leonardoward/Atlas-Sumo-Robot/3D_Models/Sumo Modelo 1.jpg

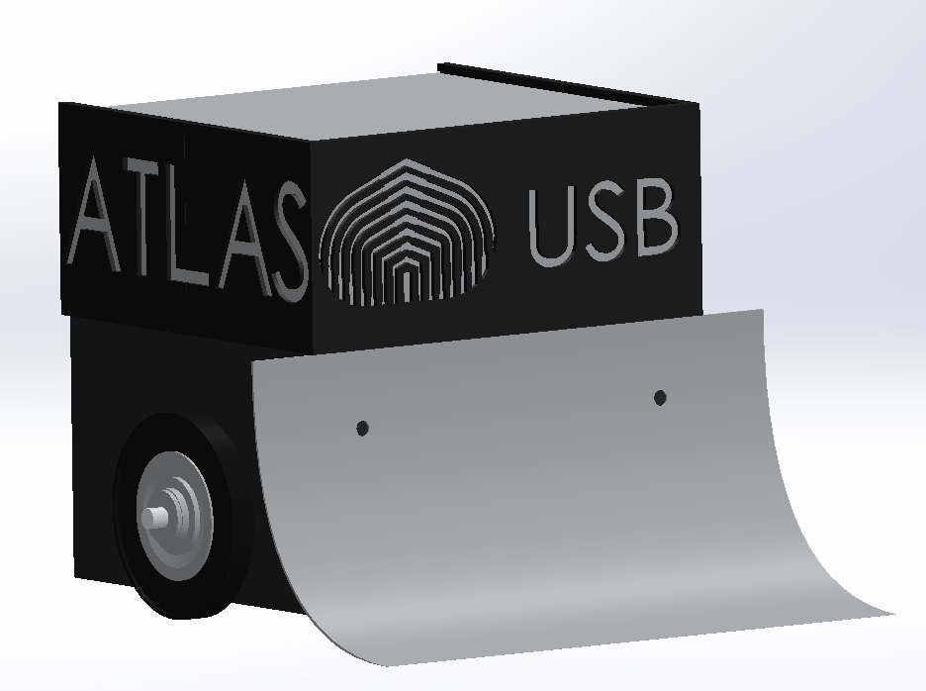
3D_Models/Sumo Modelo 1.jpg
