leonardoward/Atlas-Sumo-Robot/3D_Models/Sumo Modelo 2.jpg

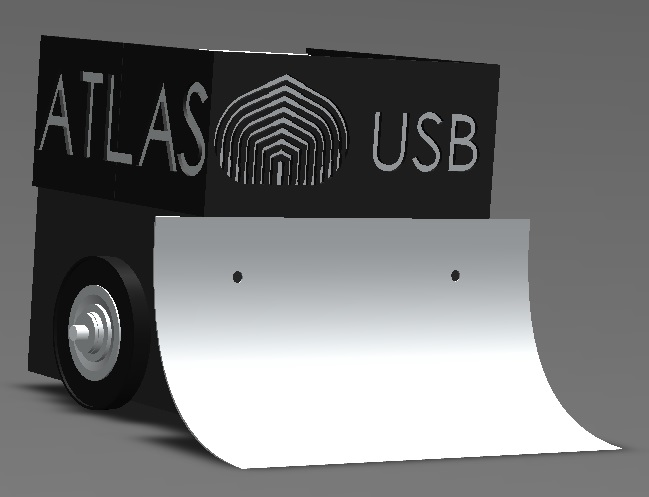
3D_Models/Sumo Modelo 2.jpg
