leonardoward/Atlas-Sumo-Robot/3D_Models/Sumo Modelo 3.jpg

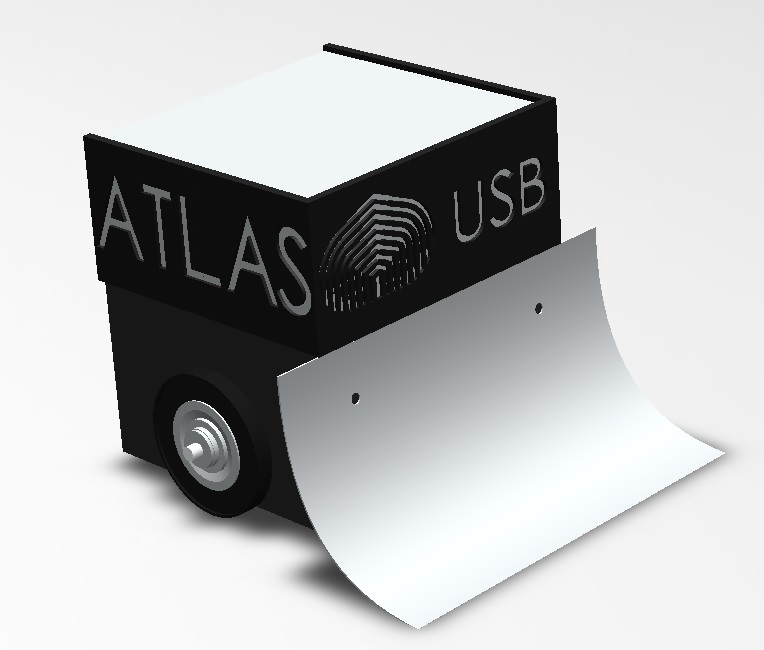
3D_Models/Sumo Modelo 3.jpg
