leonardoward/Atlas-Sumo-Robot/3D_Models/Sumo Modelo 4.jpg

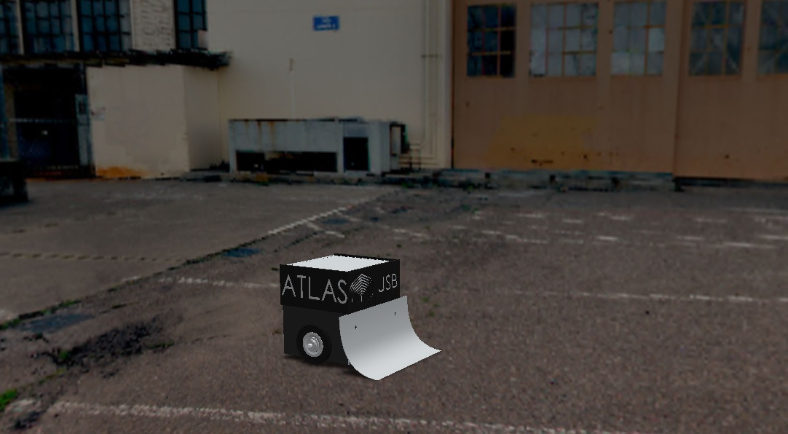
3D_Models/Sumo Modelo 4.jpg
