leonardoward/Atlas-Sumo-Robot/3D_Models/Sumo Modelo 5.jpg

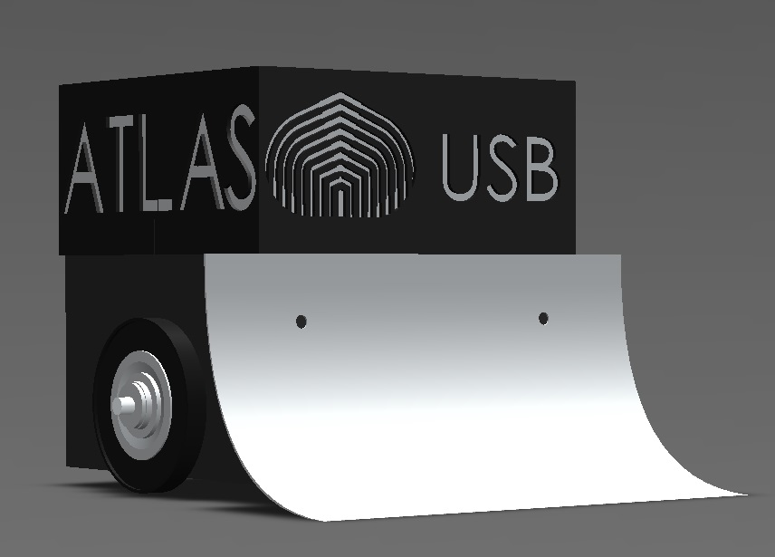
3D_Models/Sumo Modelo 5.jpg
