leonardoward/Atlas-Sumo-Robot/3D_Models/Sumo Modelo 6.jpg

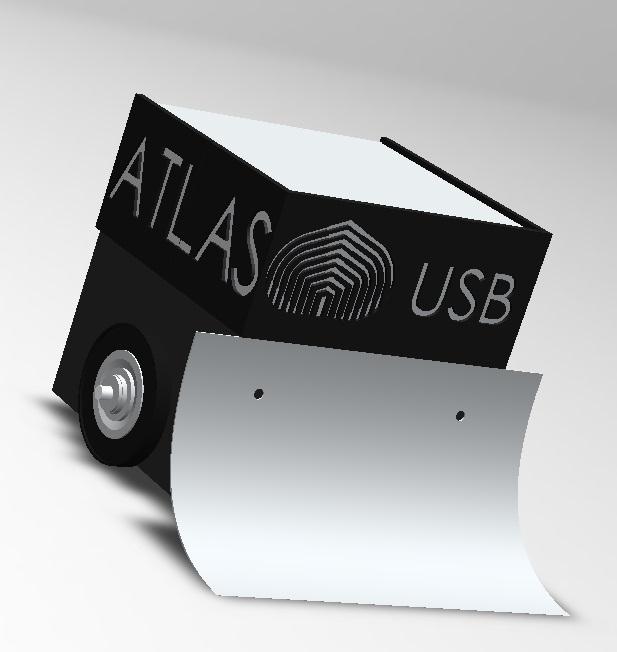
3D_Models/Sumo Modelo 6.jpg
