leonardoward/Atlas-Sumo-Robot/Pista Sumo.png

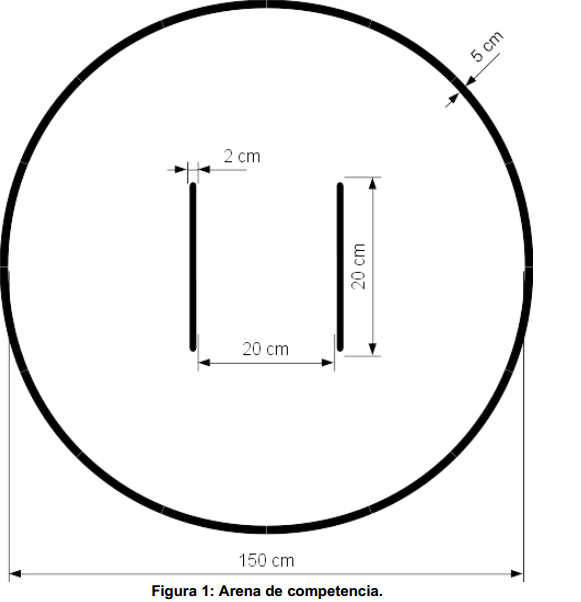
Pista Sumo.png
