leonardoward/Atlas-Sumo-Robot/3D_Models/Caja y rueda/Pieza N°3.SLDPRT

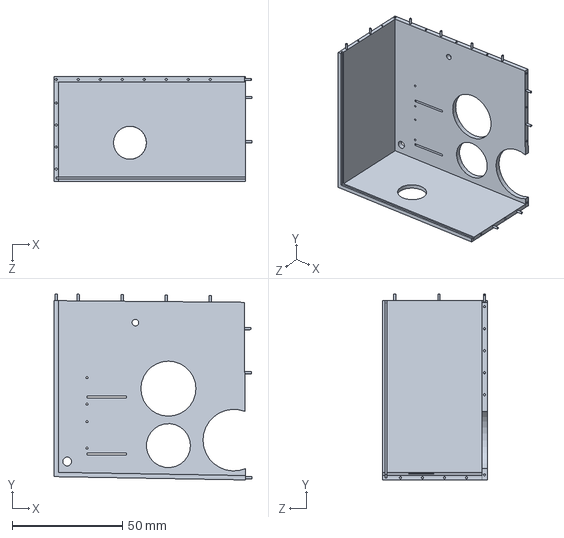
[picture p33: CAD file, 2019-05-23]
3D_Models/Caja y rueda/Pieza N°3.SLDPRT
90.0 x 84.5 x 47.5 mm
