leonardoward/Atlas-Sumo-Robot/3D_Models/Electronica/3xNanoV3.0ATmega328.SLDPRT

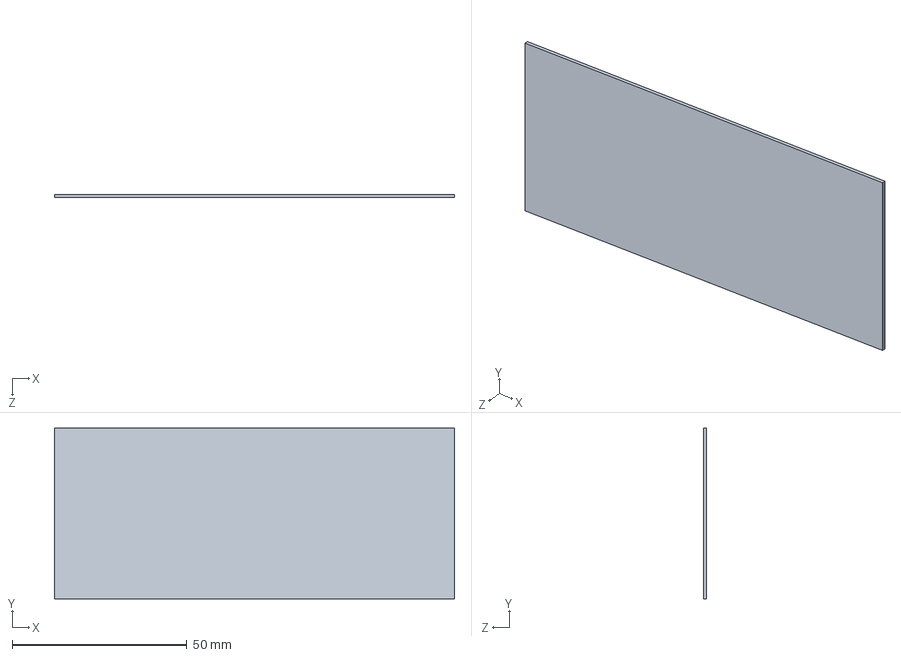
[picture p34: CAD file, 2019-05-23]
3D_Models/Electronica/3xNanoV3.0ATmega328.SLDPRT
114.3 x 48.8 x 1.00 mm
