leonardoward/Atlas-Sumo-Robot/3D_Models/Rampa Alternativa/Tubo.SLDPRT

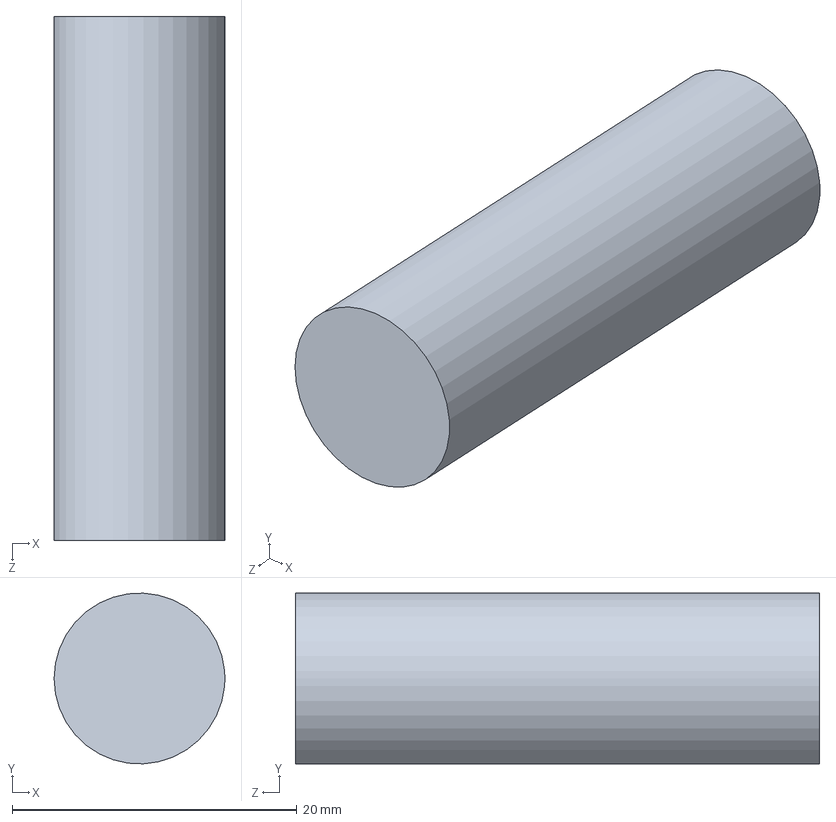
[picture p35: CAD file, 2019-05-23]
3D_Models/Rampa Alternativa/Tubo.SLDPRT
12.0 x 12.0 x 36.8 mm
