leonardoward/Atlas-Sumo-Robot/3D_Models/Version 3/EngranajeNegroCentralModificado.SLDPRT

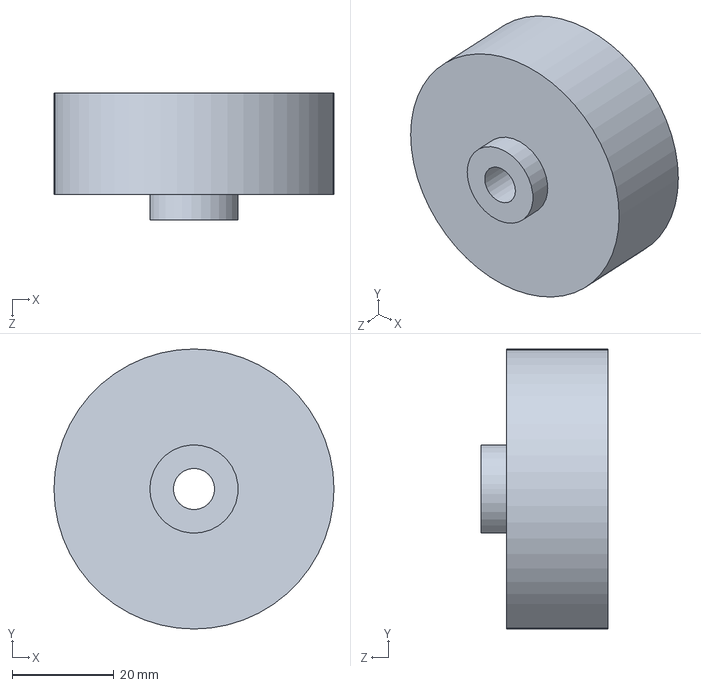
[picture p36: CAD file, 2019-05-23]
3D_Models/Version 3/EngranajeNegroCentralModificado.SLDPRT
55.0 x 55.0 x 25.0 mm
