leonardoward/Atlas-Sumo-Robot/3D_Models/Caja y rueda/Pieza N°4.SLDPRT

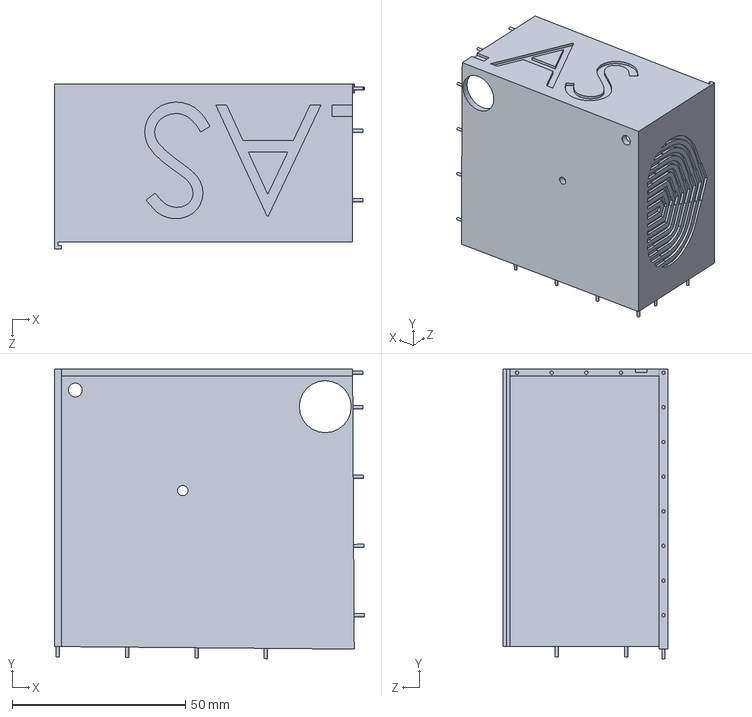
[picture p37: CAD file, 2019-05-23]
3D_Models/Caja y rueda/Pieza N°4.SLDPRT
89.4 x 83.5 x 47.5 mm
