leonardoward/Atlas-Sumo-Robot/3D_Models/Electronica/RollerBallTransfer(rueda loca).SLDPRT

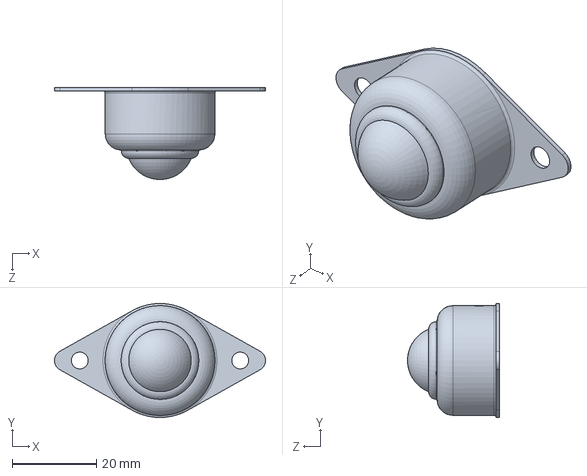
[picture p38: CAD file, 2019-05-23]
3D_Models/Electronica/RollerBallTransfer(rueda loca).SLDPRT
50.0 x 27.0 x 21.8 mm
