leonardoward/Atlas-Sumo-Robot/3D_Models/Version 3/BaseMotorDeSumo.SLDPRT

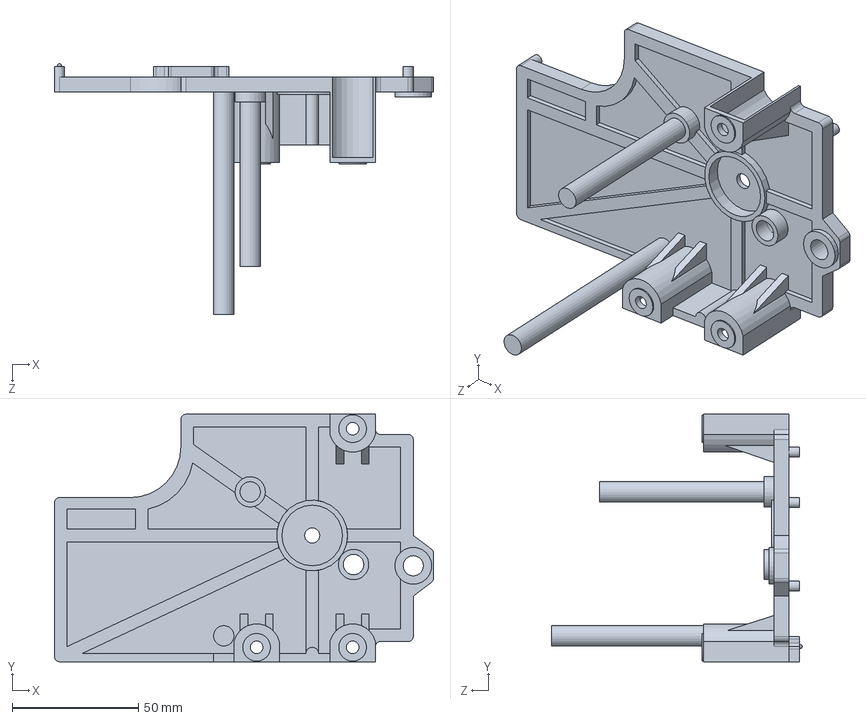
[picture p39: CAD file, 2019-05-23]
3D_Models/Version 3/BaseMotorDeSumo.SLDPRT
150.0 x 98.0 x 99.2 mm
