leonardoward/Atlas-Sumo-Robot/3D_Models/Electronica/LogicLevelShifter,4-Channel,Bidirectional.SLDPRT

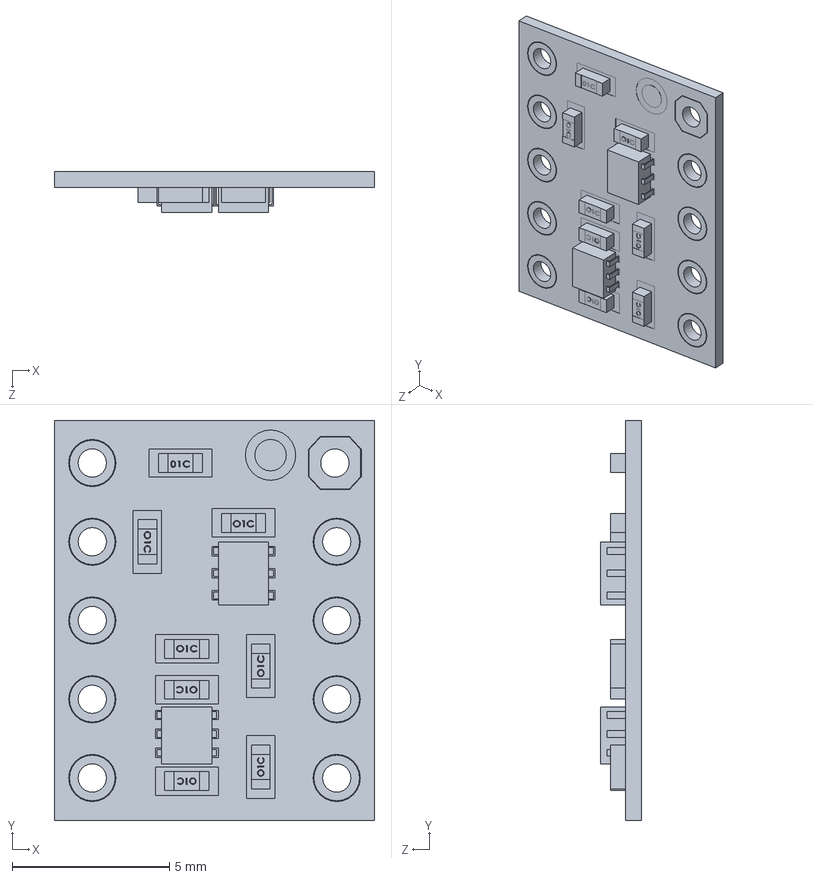
[picture p40: CAD file, 2019-05-23]
3D_Models/Electronica/LogicLevelShifter,4-Channel,Bidirectional.SLDPRT
10.2 x 12.7 x 1.30 mm
