leonardoward/Atlas-Sumo-Robot/3D_Models/Version 3/Viga.SLDPRT

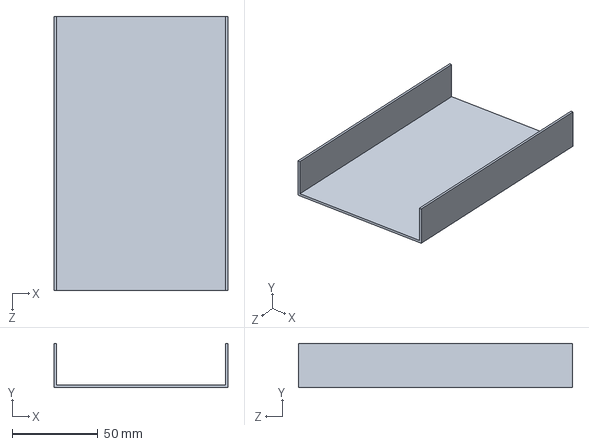
[picture p41: CAD file, 2019-05-23]
3D_Models/Version 3/Viga.SLDPRT
101.5 x 25.7 x 160.0 mm
