leonardoward/Atlas-Sumo-Robot/3D_Models/Electronica/Pololu5V,2.5AStep-DownVoltageRegulatorD24V22F5.SLDPRT

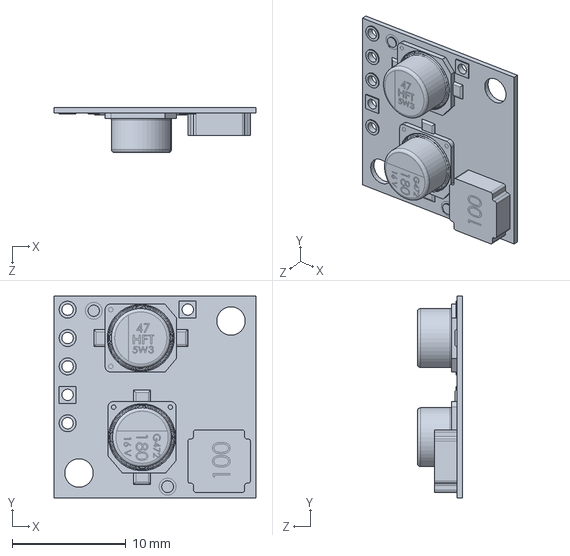
[picture p42: CAD file, 2019-05-23]
3D_Models/Electronica/Pololu5V,2.5AStep-DownVoltageRegulatorD24V22F5.SLDPRT
17.8 x 17.8 x 4.00 mm
