leonardoward/Atlas-Sumo-Robot/3D_Models/Version 3/MotorDeSumo.SLDPRT

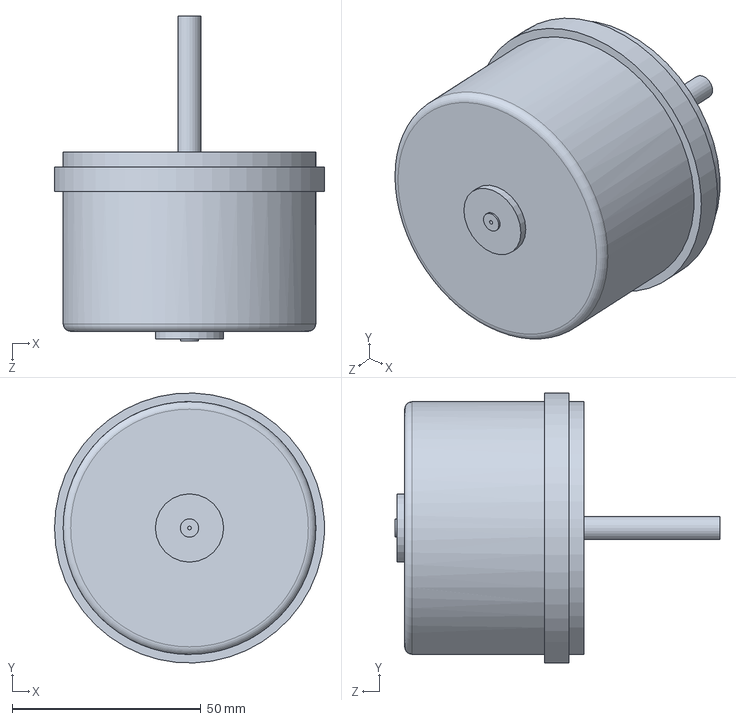
[picture p43: CAD file, 2019-05-23]
3D_Models/Version 3/MotorDeSumo.SLDPRT
71.5 x 71.5 x 86.0 mm
