leonardoward/Atlas-Sumo-Robot/3D_Models/Electronica/QTR-1AReflectanceSensor.SLDPRT

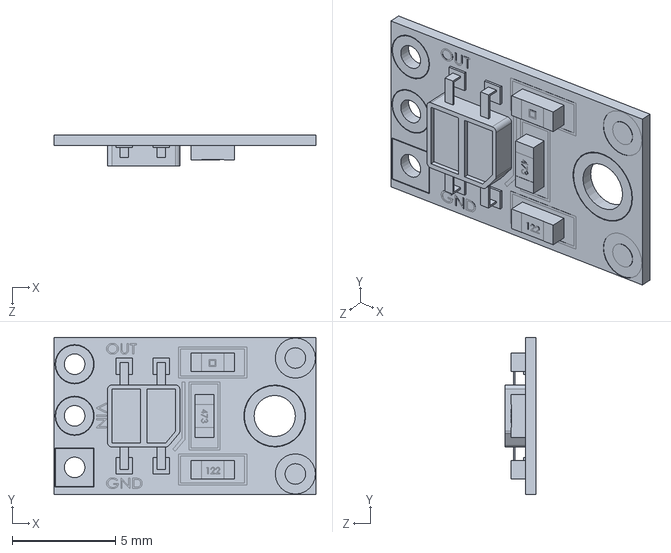
[picture p44: CAD file, 2019-05-23]
3D_Models/Electronica/QTR-1AReflectanceSensor.SLDPRT
12.7 x 7.62 x 1.50 mm
