leonardoward/Atlas-Sumo-Robot/3D_Models/Version 3/RuedaNueva.SLDPRT

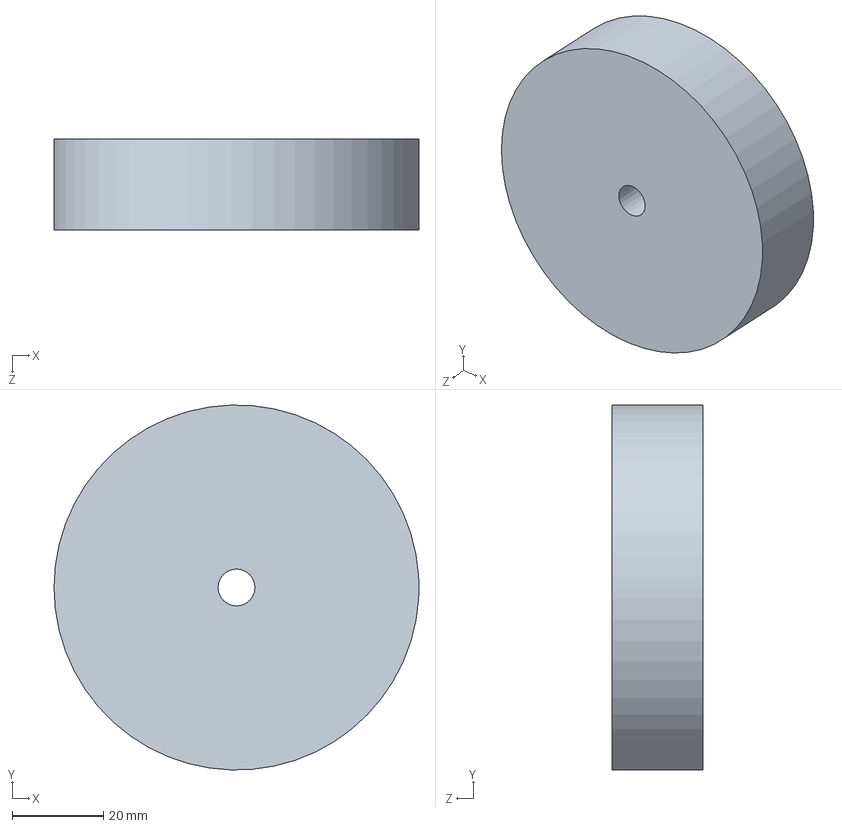
[picture p45: CAD file, 2019-05-23]
3D_Models/Version 3/RuedaNueva.SLDPRT
80.0 x 80.0 x 20.0 mm
