leonardoward/Atlas-Sumo-Robot/3D_Models/Electronica/PololuAdjustable9-30VStep-UpVoltageRegulatorU3V50AHV.SLDPRT

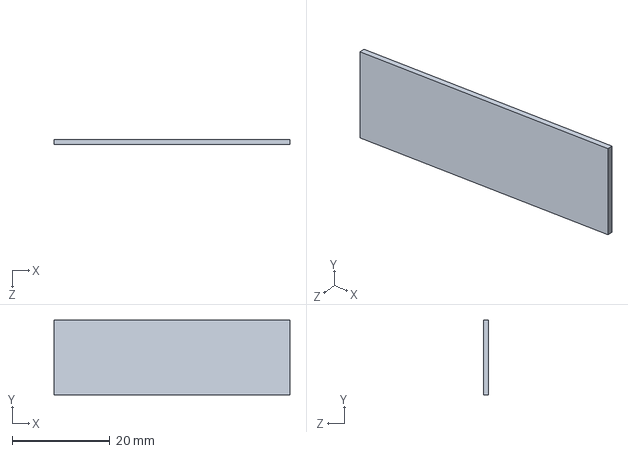
[picture p46: CAD file, 2019-05-23]
3D_Models/Electronica/PololuAdjustable9-30VStep-UpVoltageRegulatorU3V50AHV.SLDPRT
48.3 x 15.2 x 1.00 mm
