leonardoward/Atlas-Sumo-Robot/3D_Models/Electronica/LiPoBattery.SLDPRT

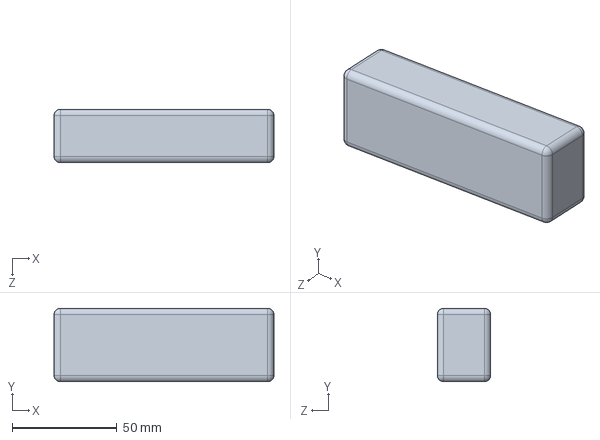
[picture p47: CAD file, 2019-05-23]
3D_Models/Electronica/LiPoBattery.SLDPRT
104.8 x 34.9 x 25.4 mm
