leonardoward/Atlas-Sumo-Robot/Electronics_Design/Electronica/Pololu step-up voltage regulator U3V50x, bottom view with dimensions.jpg

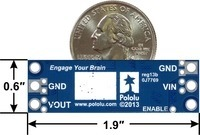
Electronics_Design/Electronica/Pololu step-up voltage regulator U3V50x, bottom view with dimensions.jpg
