leonardoward/Atlas-Sumo-Robot/3D_Models/Version 3/PDF/2.Chasis2.PDF

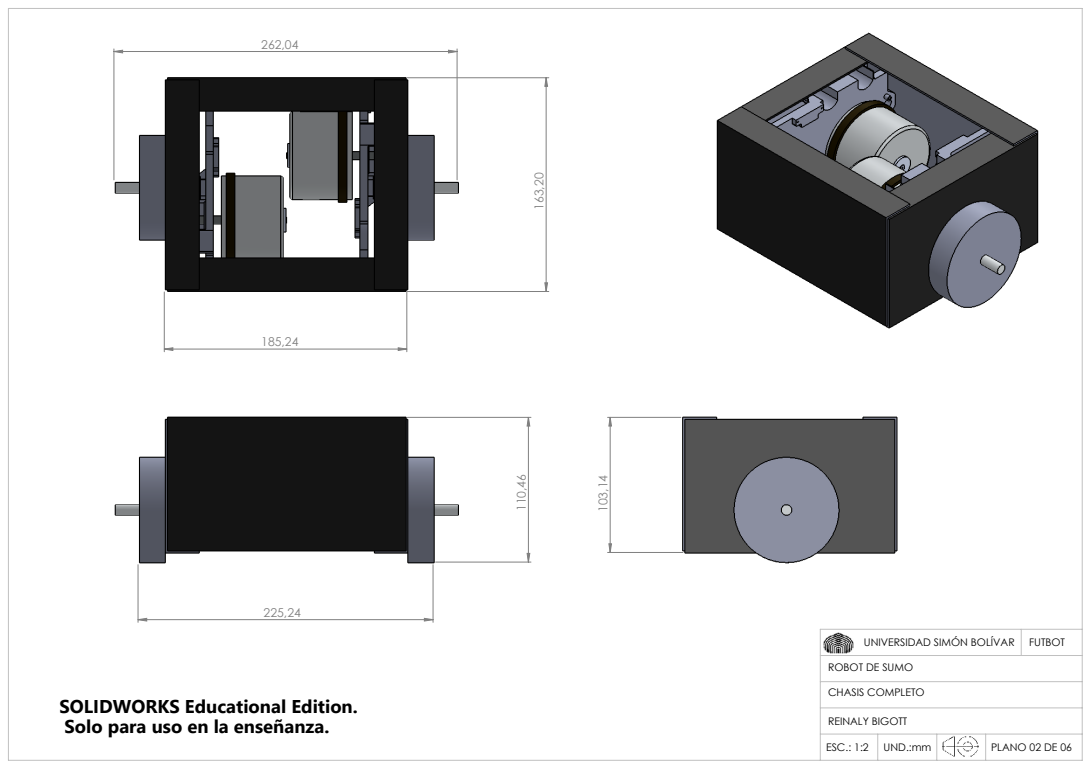
[picture p62: page 1]
UNIVERSIDAD SIMÓN BOLÍVAR; FUTBOT; REINALY BIGOTT; ESC.: 1:2; UND.:mm; PLANO 02 DE 06

ROBOT DE SUMO
CHASIS COMPLETO

SOLIDWORKS Educational Edition.
Solo para uso en la enseñanza.
