leonardoward/Atlas-Sumo-Robot/3D_Models/Version 3/PDF/3.Chasis3.PDF

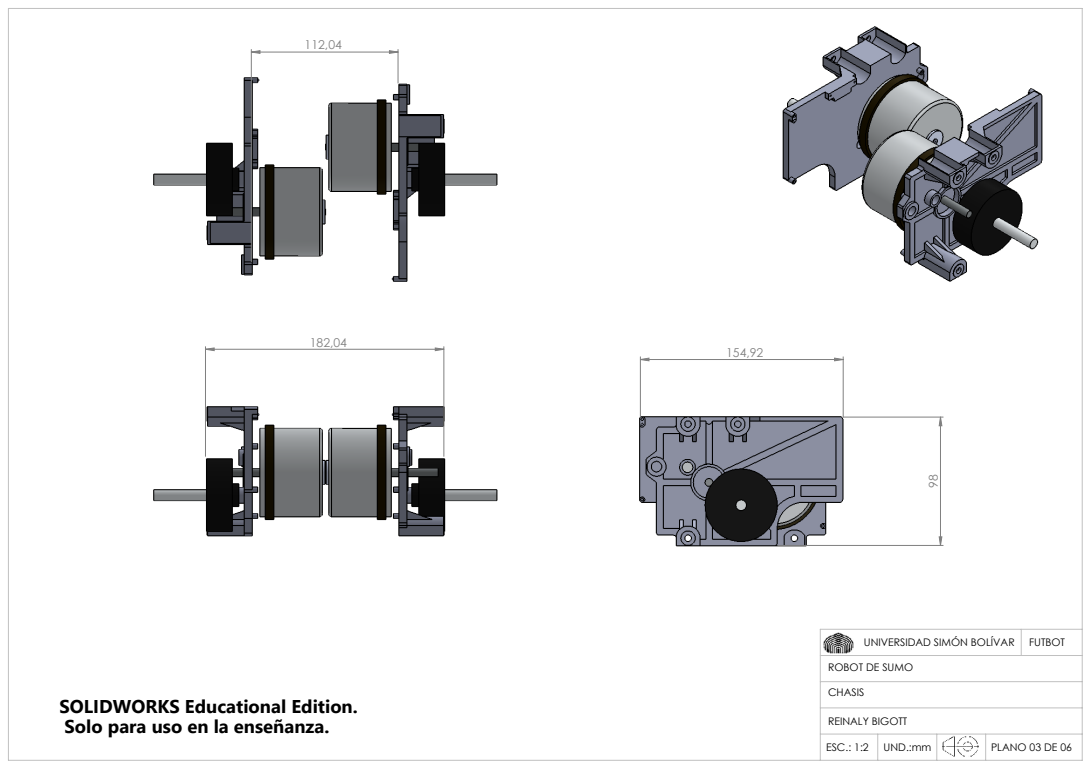
[picture p63: page 1]
UNIVERSIDAD SIMÓN BOLÍVAR; FUTBOT; REINALY BIGOTT; ESC.: 1:2; UND.:mm; PLANO 03 DE 06

ROBOT DE SUMO
CHASIS

SOLIDWORKS Educational Edition.
Solo para uso en la enseñanza.
