leonardoward/Atlas-Sumo-Robot/3D_Models/Version 3/PDF/4.PlanoVigaLateral.PDF

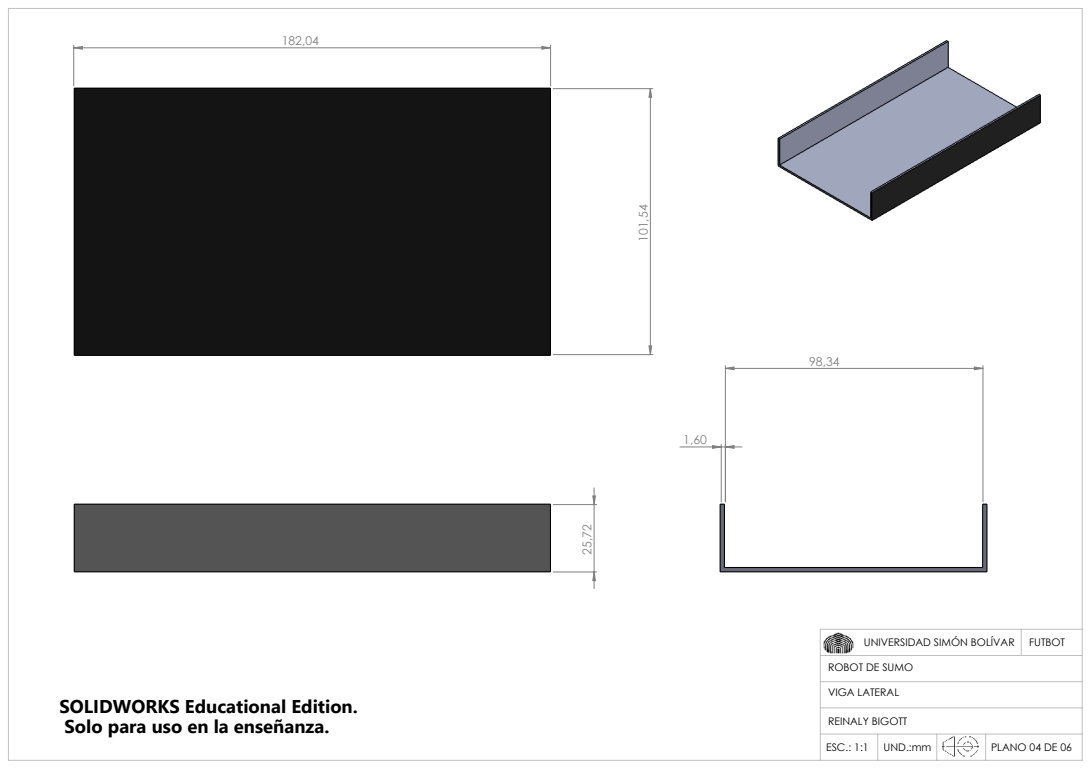
[picture p64: page 1]
UNIVERSIDAD SIMÓN BOLÍVAR; FUTBOT; REINALY BIGOTT; ESC.: 1:1; UND.:mm; PLANO 04 DE 06

ROBOT DE SUMO
VIGA LATERAL

SOLIDWORKS Educational Edition.
Solo para uso en la enseñanza.
