leonardoward/Atlas-Sumo-Robot/3D_Models/Version 3/PDF/5.PlanoViga.PDF

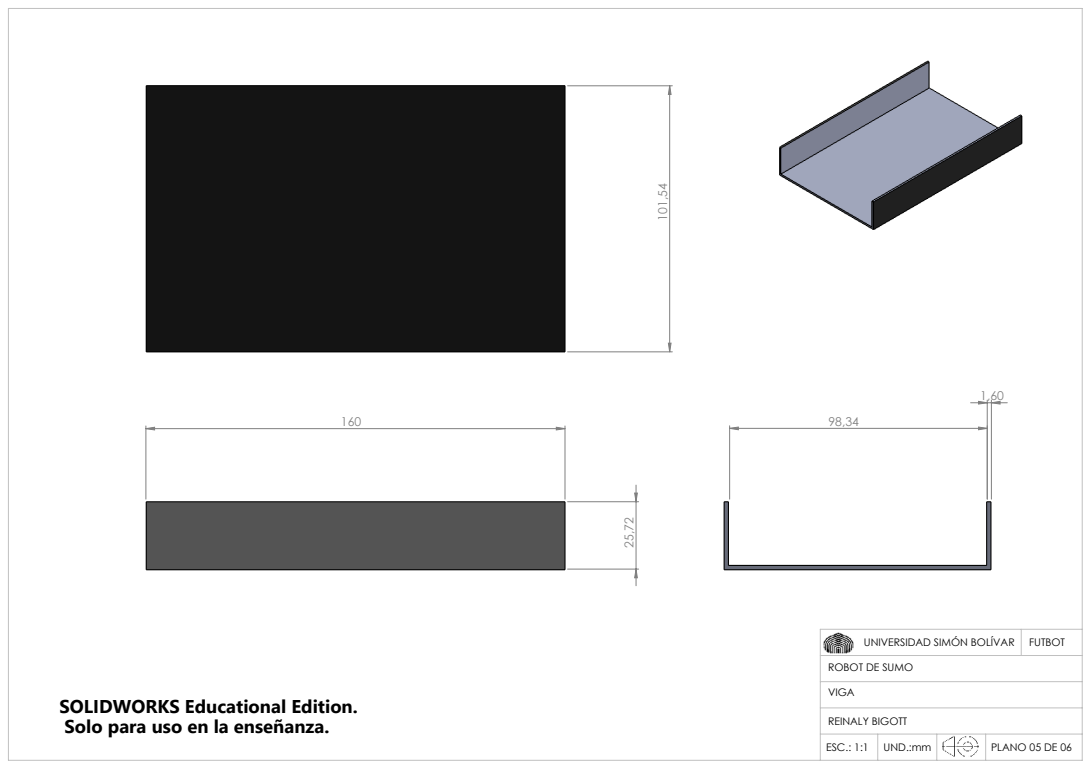
[picture p65: page 1]
UNIVERSIDAD SIMÓN BOLÍVAR; FUTBOT; REINALY BIGOTT; ESC.: 1:1; UND.:mm; PLANO 05 DE 06

ROBOT DE SUMO
VIGA

SOLIDWORKS Educational Edition.
Solo para uso en la enseñanza.
