leonardoward/Atlas-Sumo-Robot/3D_Models/Version 3/PDF/6.PlanoRuedaNuevo.PDF

UNIVERSIDAD SIMÓN BOLÍVAR; FUTBOT; REINALY BIGOTT; ESC.: 2:1; UND.:mm; PLANO 06 DE 06

ROBOT DE SUMO
RUEDA

SOLIDWORKS Educational Edition.
Solo para uso en la enseñanza.
