leonardoward/Atlas-Sumo-Robot/3D_Models/Version 2/RobotSumo/Planos/3 PlanoMotor.PDF

UNIVERSIDAD SIMÓN BOLÍVAR; FUTBOT; REINALY BIGOTT; ESC.: 1:1; UND.:mm; PLANO 03 DE 10

ROBOT DE SUMO
MOTOR

SOLIDWORKS Educational Edition.
Solo para uso en la enseñanza.
