leonardoward/Atlas-Sumo-Robot/3D_Models/Version 2/RobotSumo/Planos/7 PlanoRueda.PDF

SECCIÓN A-A; UNIVERSIDAD SIMÓN BOLÍVAR; FUTBOT; REINALY BIGOTT; ESC.: 1:1; UND.:mm; PLANO 07 DE 10

ROBOT DE SUMO
RUEDAS

SOLIDWORKS Educational Edition.
Solo para uso en la enseñanza.
