leonardoward/Atlas-Sumo-Robot/3D_Models/Version 2/RobotSumo/Planos/9 PlanoLaminaInferior.PDF

UNIVERSIDAD SIMÓN BOLÍVAR; FUTBOT; REINALY BIGOTT; ESC.: 1:1; UND.:mm; PLANO 09 DE 10

ROBOT DE SUMO
LAMINA INFERIOR

SOLIDWORKS Educational Edition.
Solo para uso en la enseñanza.
