leonardoward/Atlas-Sumo-Robot/Electronics_Design/Sumo.sch

## KiCad design Electronics_Design/Sumo.sch (2019-05-23)

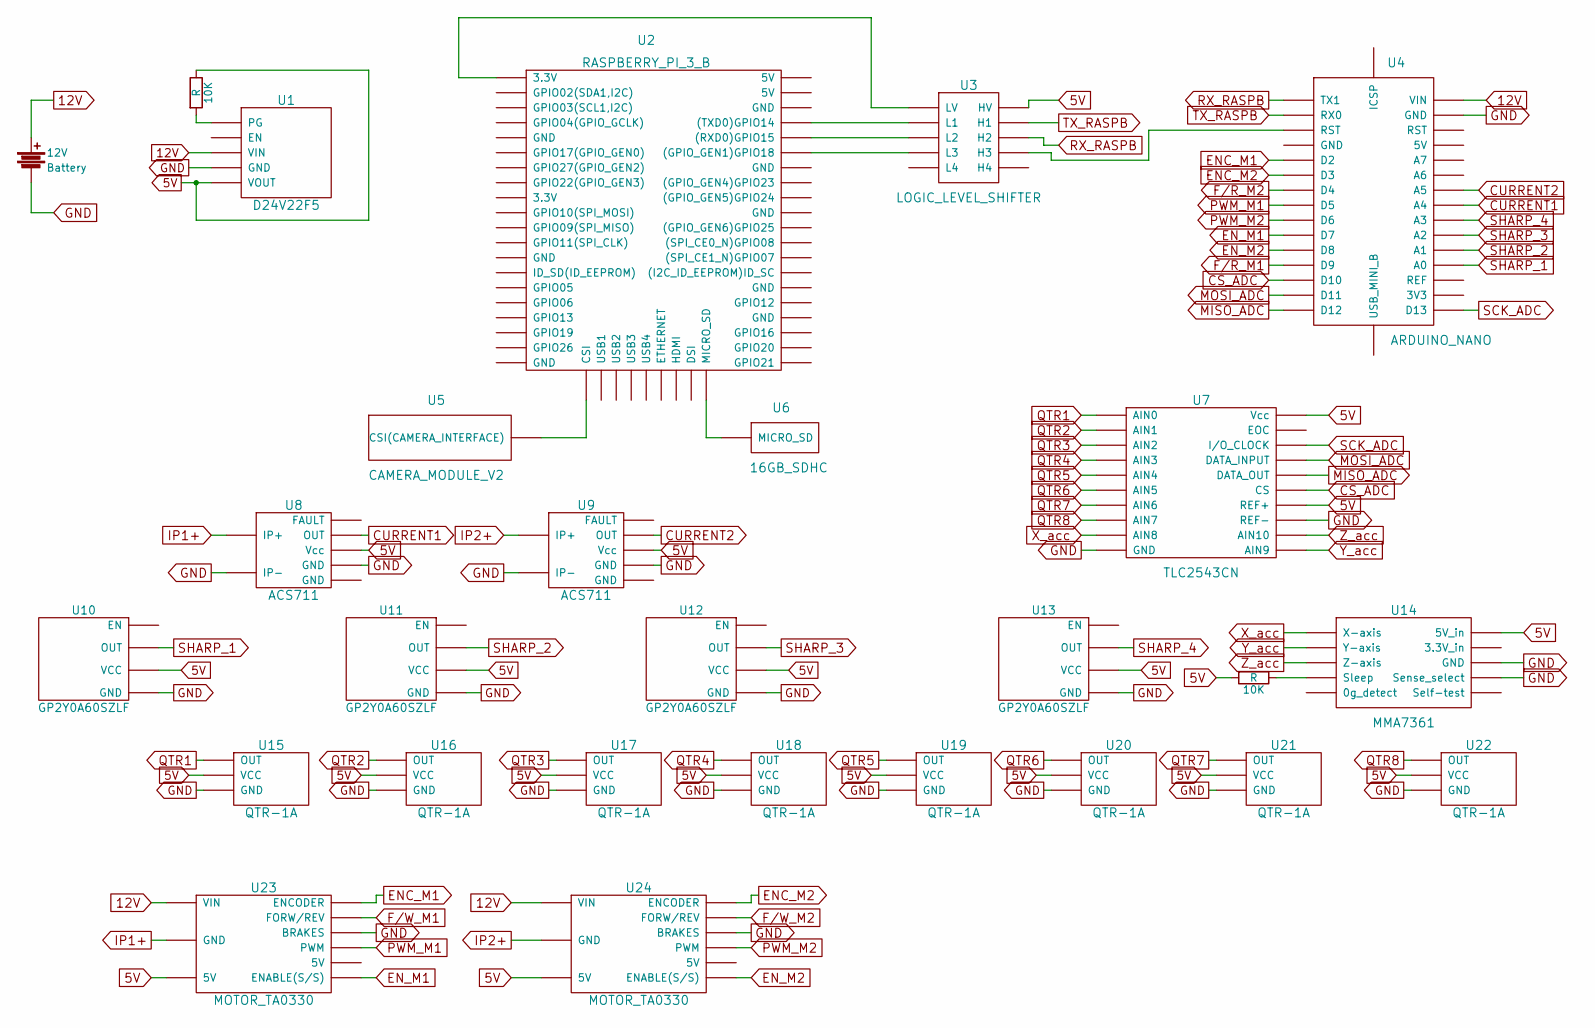
[picture p70: schematic Sumo.sch]

Parts:
10K: R
12V: Battery
U1: D24V22F5
U2: RASPBERRY_PI_3_B
U3: LOGIC_LEVEL_SHIFTER
U4: ARDUINO_NANO
U5: CAMERA_MODULE_V2
U6: 16GB_SDHC
U7: TLC2543CN
U8, U9: ACS711
U10, U11, U12, U13: GP2Y0A60SZLF
U14: MMA7361
U15, U16, U17, U18, U19, U20, U21, U22: QTR-1A
U23, U24: MOTOR_TA0330

Connections:
5V: 10K.1, 10K.2, U1.~, U3.~, U7.~, U8.~, U9.~, U10.~, U11.~, U12.~, U13.~, U14.~, U15.~, U16.~, U17.~, U18.~, U19.~, U20.~, U21.~, U22.~, U23.~, U24.~
12V: 12V.1, U1.~, U4.~, U23.~, U24.~
CS_ADC: U4.~, U7.~
CURRENT1: U4.~, U8.~
CURRENT2: U4.~, U9.~
ENC_M1: U4.~, U23.~
ENC_M2: U4.~, U24.~
EN_M1: U4.~, U23.~
EN_M2: U4.~, U24.~
F/R_M1: U4.~
F/R_M2: U4.~
F/W_M1: U23.~
F/W_M2: U24.~
GND: 12V.2, U1.~, U4.~, U7.~, U8.~, U9.~, U10.~, U11.~, U12.~, U13.~, U14.~, U15.~, U16.~, U17.~, U18.~, U19.~, U20.~, U21.~, U22.~, U23.~, U24.~
IP1+: U8.~, U23.~
IP2+: U9.~, U24.~
MISO_ADC: U4.~, U7.~
MOSI_ADC: U4.~, U7.~
unnamed: 10K.1, U14.~
unnamed: 10K.2, U1.~
unnamed: U2.~, U3.~, U5.~, U6.~
unnamed: U3.~, U4.~
PWM_M1: U4.~, U23.~
PWM_M2: U4.~, U24.~
QTR1: U7.~, U15.~
QTR2: U7.~, U16.~
QTR3: U7.~, U17.~
QTR4: U7.~, U18.~
QTR5: U7.~, U19.~
QTR6: U7.~, U20.~
QTR7: U7.~, U21.~
QTR8: U7.~, U22.~
RX_RASPB: U3.~, U4.~
SCK_ADC: U4.~, U7.~
SHARP_1: U4.~, U10.~
SHARP_2: U4.~, U11.~
SHARP_3: U4.~, U12.~
SHARP_4: U4.~, U13.~
TX_RASPB: U3.~, U4.~
X_acc: U7.~, U14.~
Y_acc: U7.~, U14.~
Z_acc: U7.~, U14.~
