leonardoward/Atlas-Sumo-Robot/arduino/Software_Sumo/Acelerometro.ino

//######################################################################################################################
//##                                                  Acelerometro                                                    ##
//######################################################################################################################
float getAxis_adcExt(int axis){
  switch(axis){
    case 1: //X Axis
      return x_acc;
    case 2: //Y Axis
      return y_acc;
    case 3: //Z Axis
      return z_acc;
  }
}
