leonardoward/Atlas-Sumo-Robot/arduino/Software_Sumo/Linea.ino

//######################################################################################################################
//##                                           Detectores de Línea                                                    ##
//######################################################################################################################
/*
void measure_lineDetect(){

}
char getVal_lineDetect(int lineDetect){

}
*/
